Epicjoy/SC64/assets/7.jpg

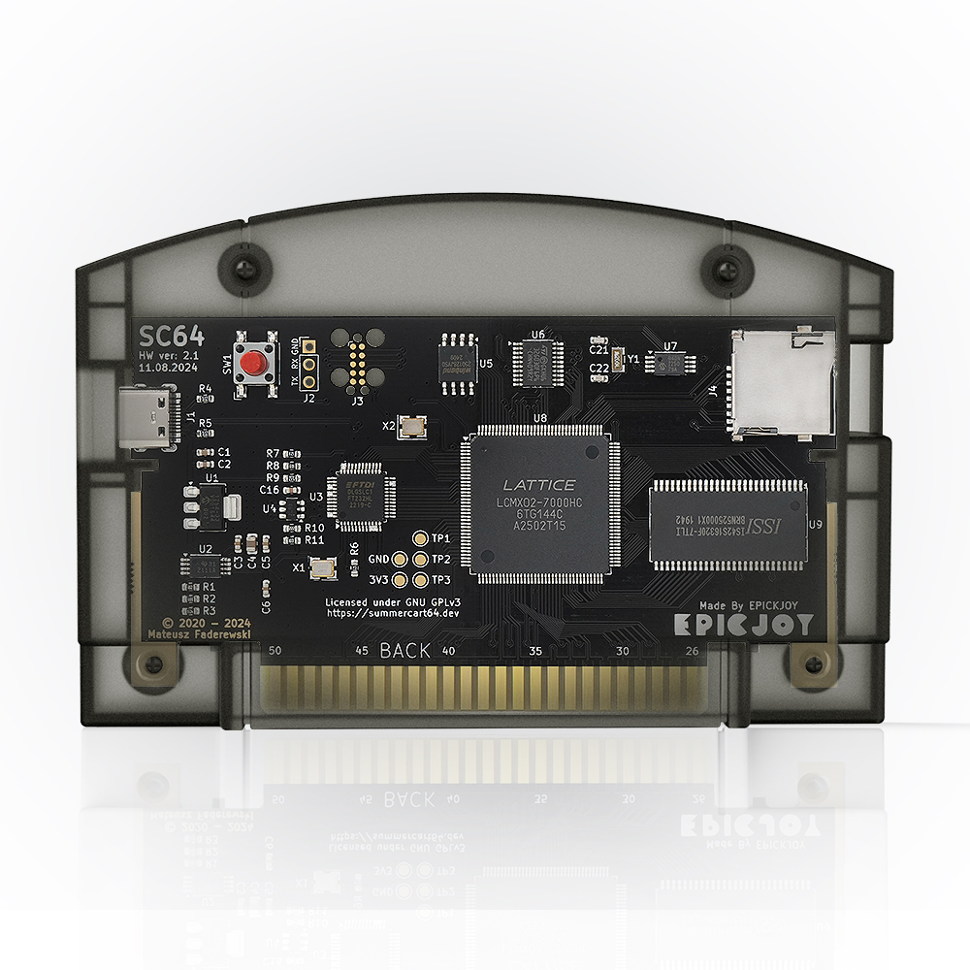
assets/7.jpg
